JGAguado/LIA/enclosure/V1.0-Detachable/renders/explode-view.jpg

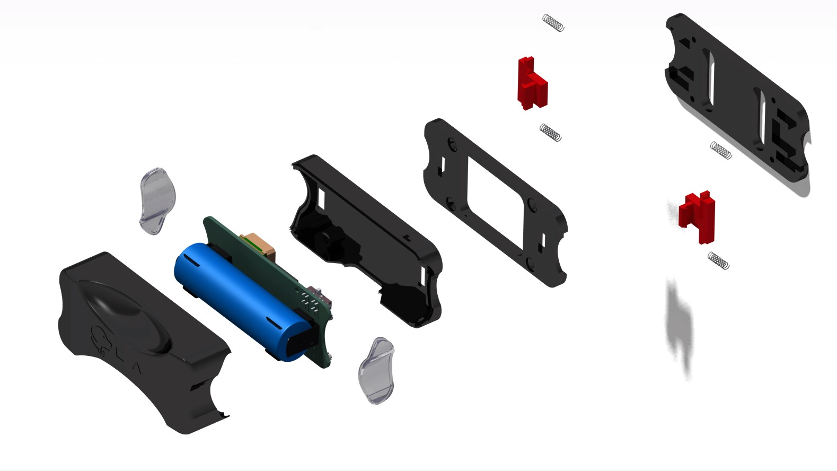
enclosure/V1.0-Detachable/renders/explode-view.jpg
