JGAguado/LIA/enclosure/V1.1-Fixed/renders/explode-view.jpg

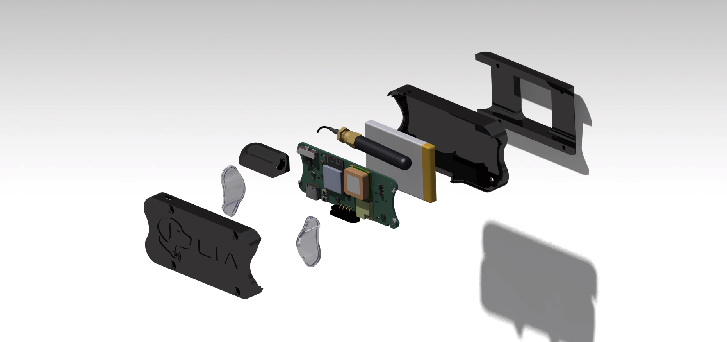
enclosure/V1.1-Fixed/renders/explode-view.jpg
