JGAguado/LIA/website/src/assets/brand/Primary dark.png

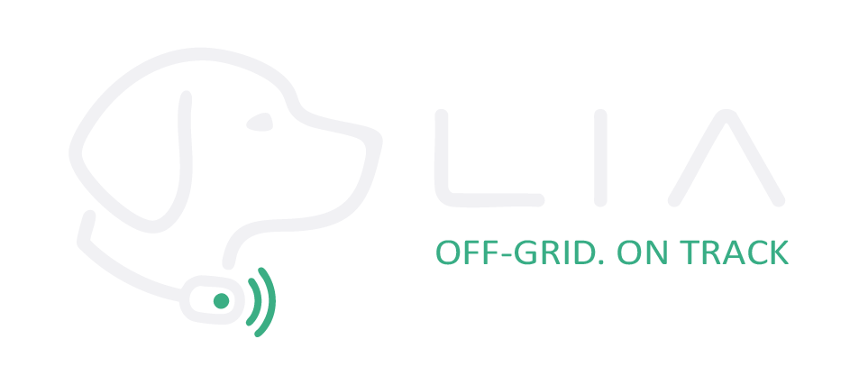
website/src/assets/brand/Primary dark.png
