JGAguado/LIA/website/src/assets/photos/6003601369522179307.jpg

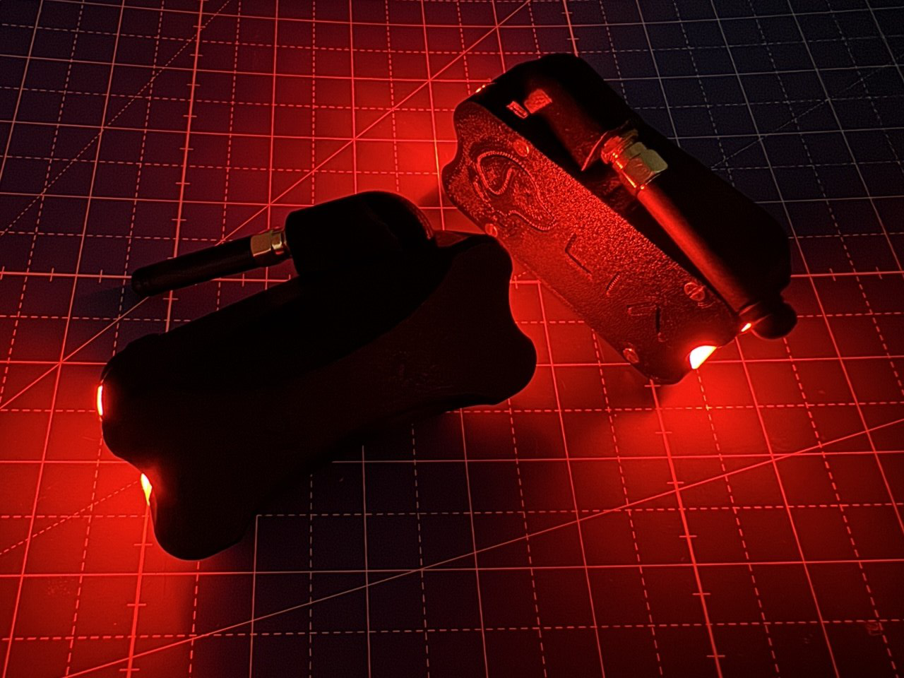
website/src/assets/photos/6003601369522179307.jpg
