JGAguado/LIA/website/src/assets/photos/6003601369522179308.jpg

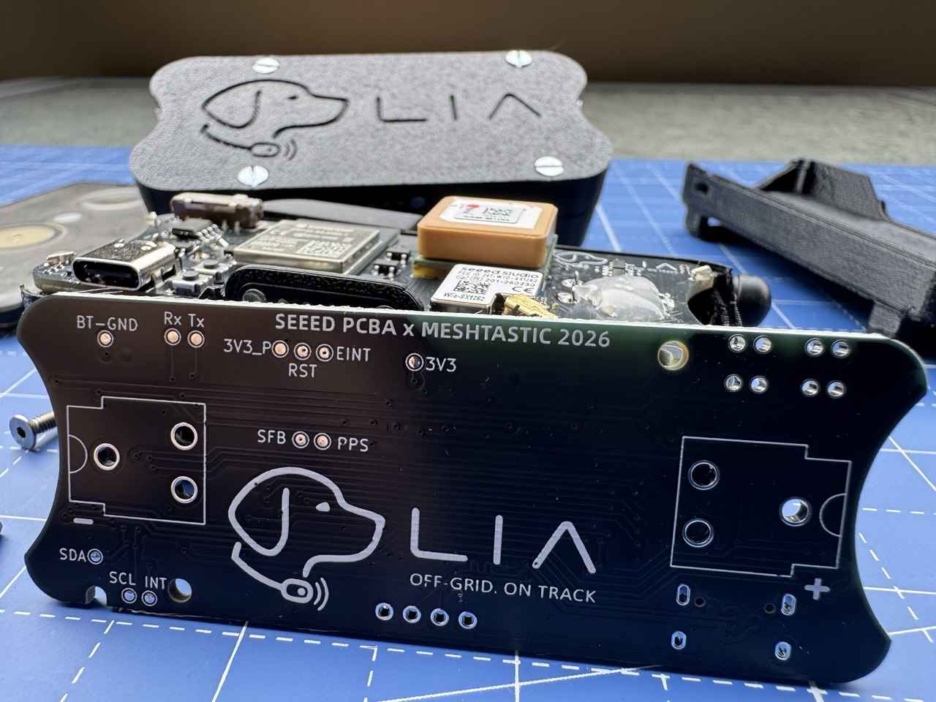
website/src/assets/photos/6003601369522179308.jpg
