JGAguado/LIA/website/src/assets/photos/6003601369522179309.jpg

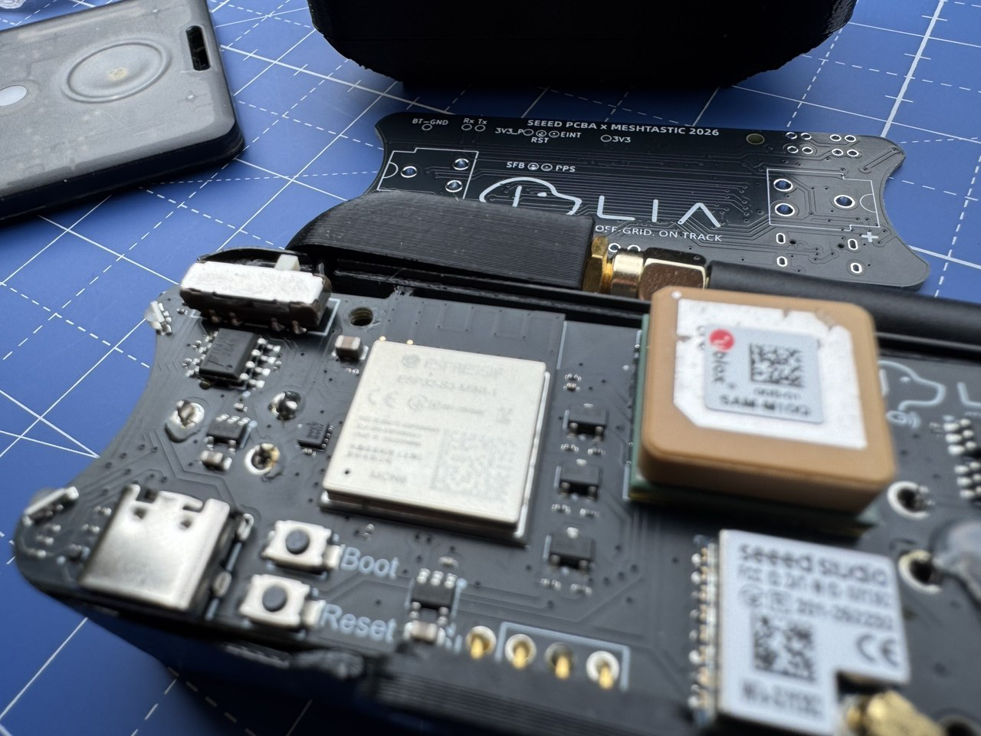
website/src/assets/photos/6003601369522179309.jpg
