JGAguado/LIA/website/src/assets/photos/6003601369522179310.jpg

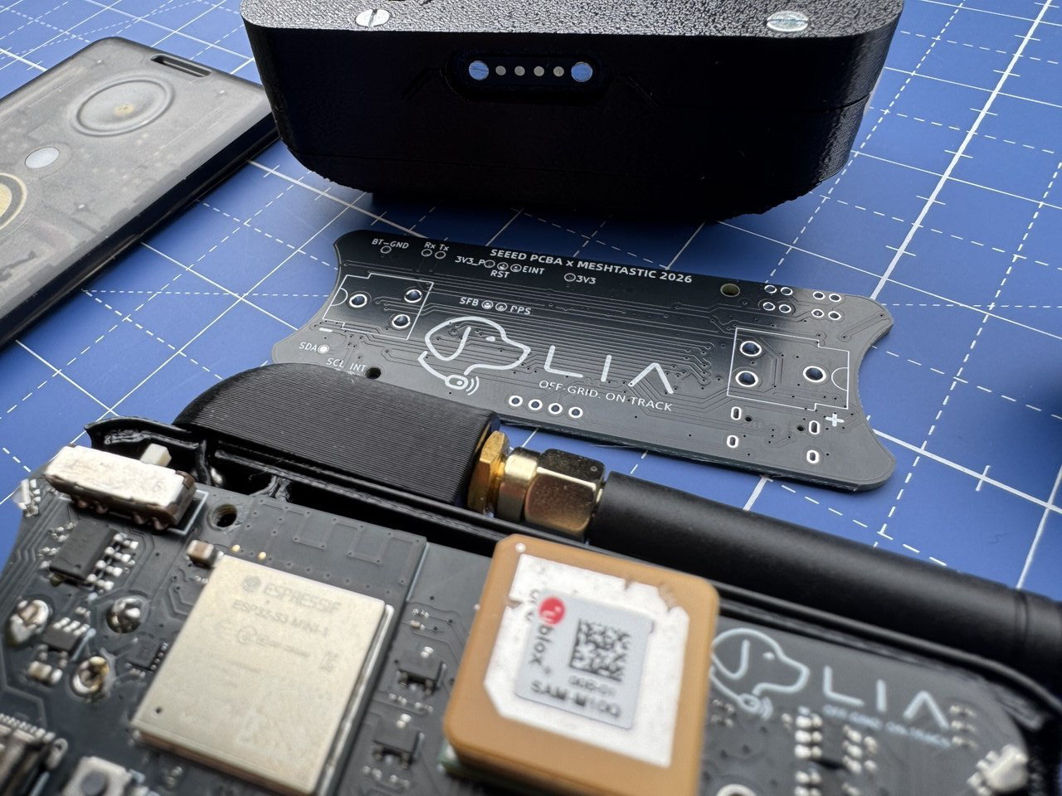
website/src/assets/photos/6003601369522179310.jpg
