JGAguado/LIA/website/src/assets/photos/6003601369522179314.jpg

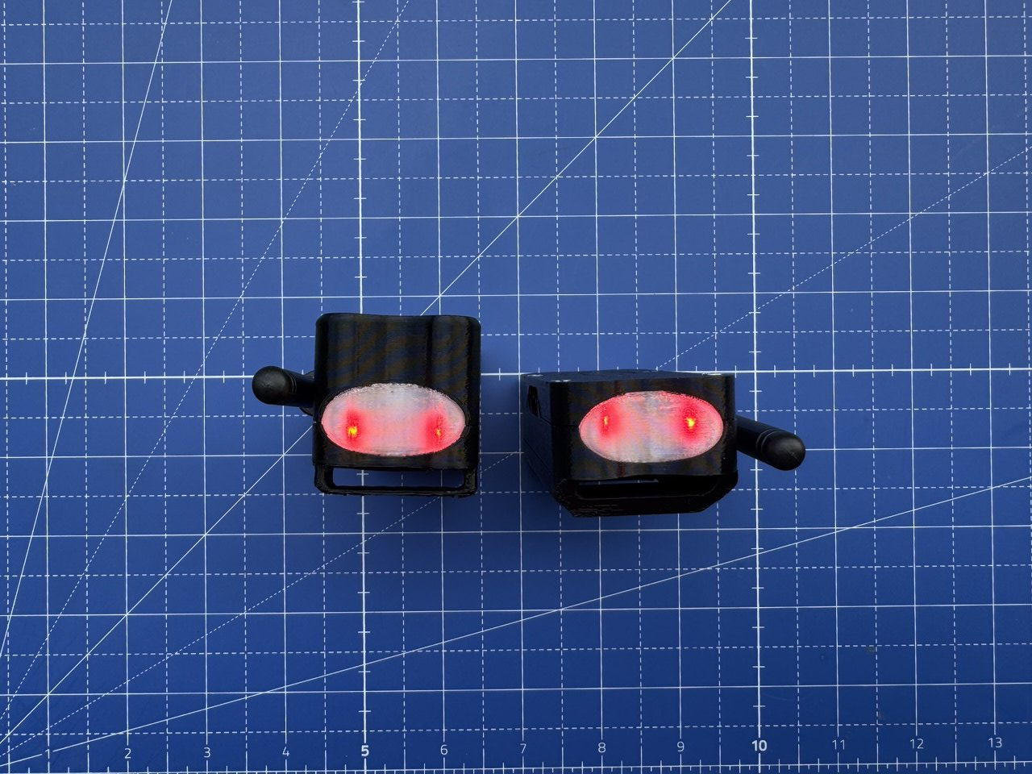
website/src/assets/photos/6003601369522179314.jpg
