JGAguado/LIA/website/src/assets/photos/6003601369522179320.jpg

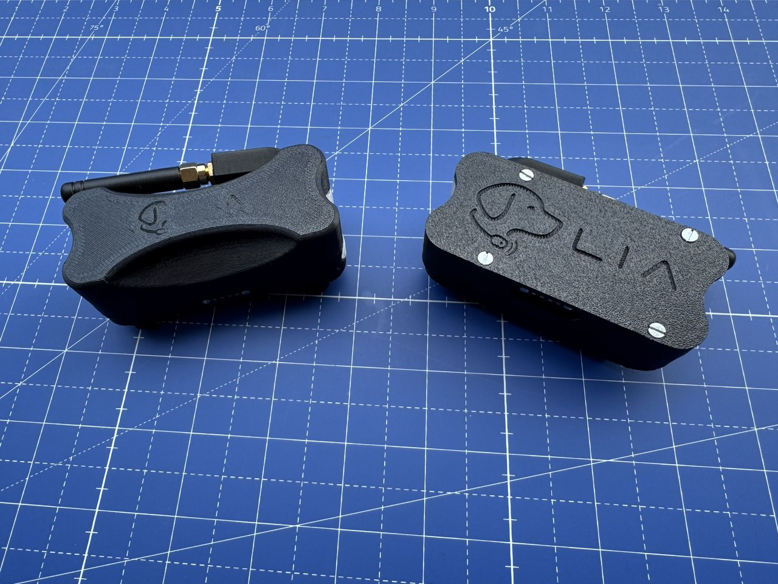
website/src/assets/photos/6003601369522179320.jpg
