JGAguado/LIA/website/src/assets/photos/6003601369522179321.jpg

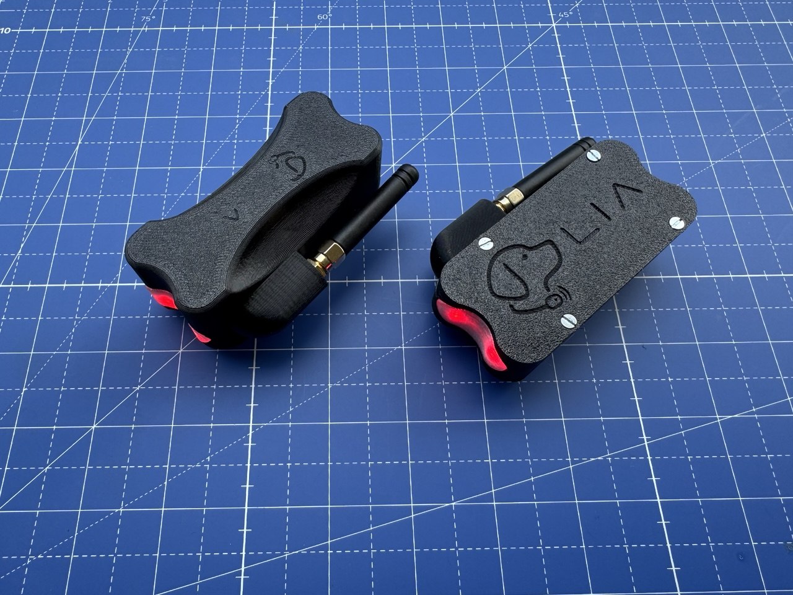
website/src/assets/photos/6003601369522179321.jpg
