JGAguado/LIA/website/src/assets/photos/Features/Beacon.jpg

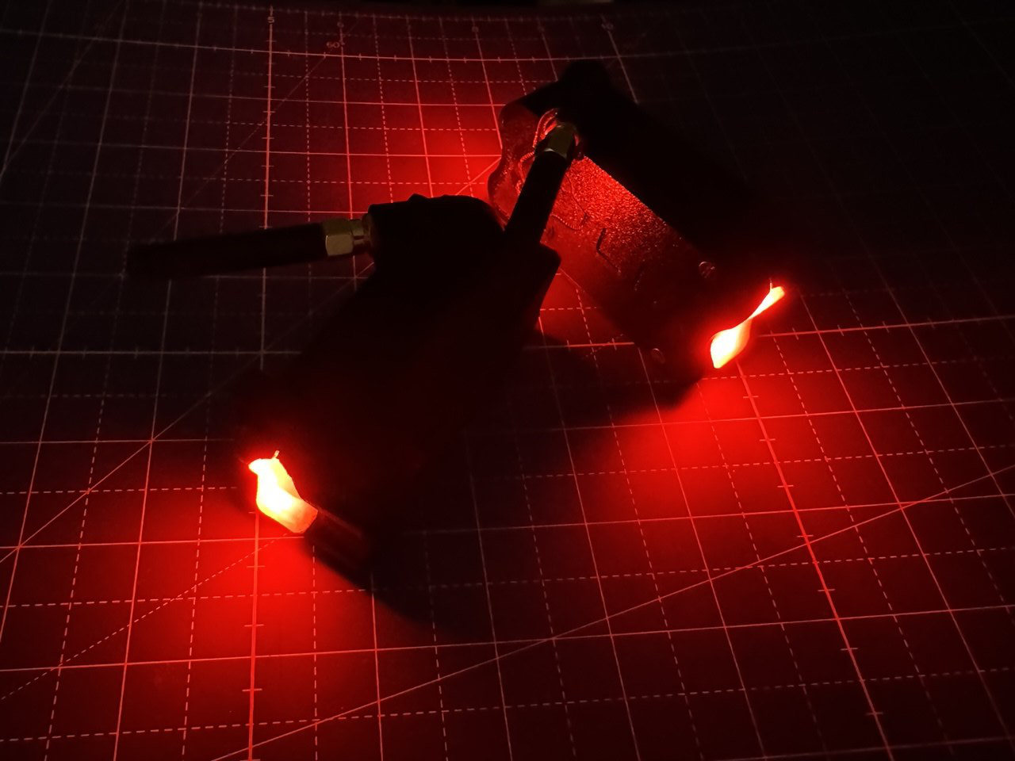
website/src/assets/photos/Features/Beacon.jpg
