JGAguado/LIA/website/src/assets/photos/Features/GPS.jpg

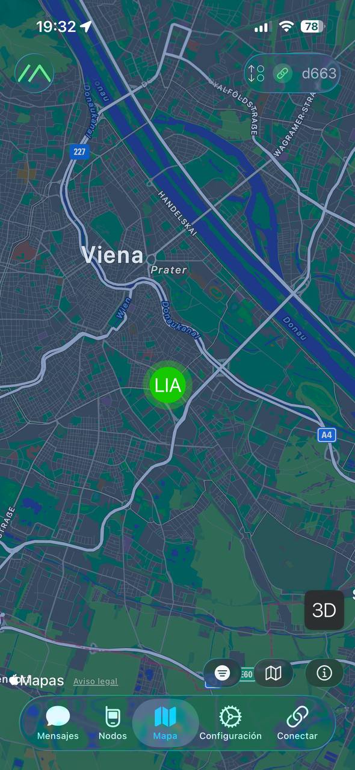
website/src/assets/photos/Features/GPS.jpg
