JGAguado/LIA/website/src/assets/photos/Features/Meshtastic.jpg

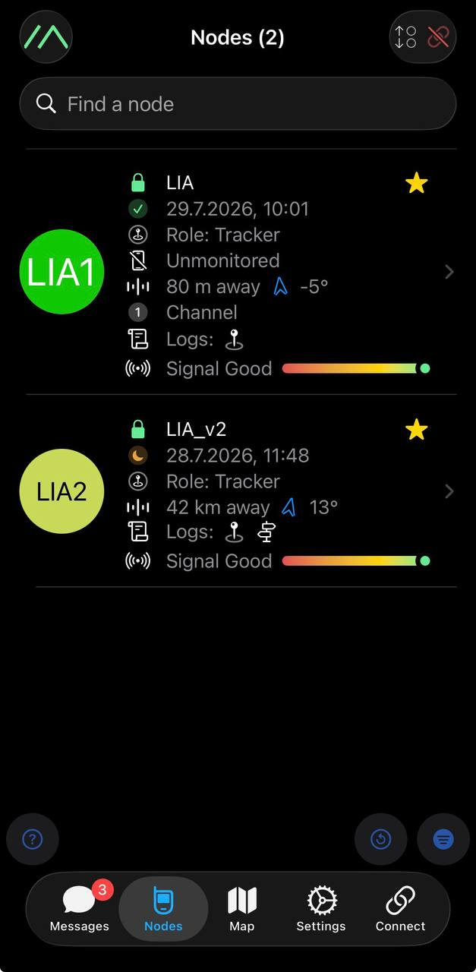
website/src/assets/photos/Features/Meshtastic.jpg
