JGAguado/LIA/website/src/assets/photos/Features/OpenSource.jpg

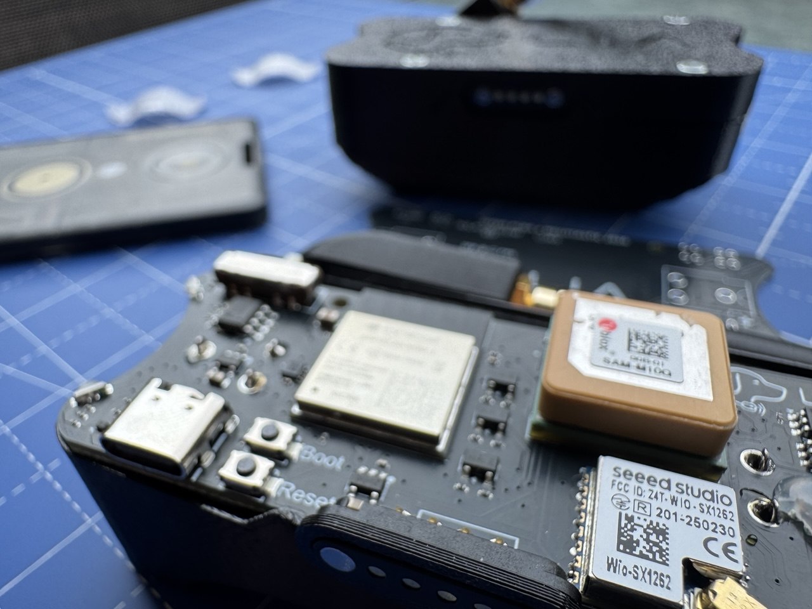
website/src/assets/photos/Features/OpenSource.jpg
