JGAguado/LIA/enclosure/V1.0-Detachable/renders/assembly-2.jpg

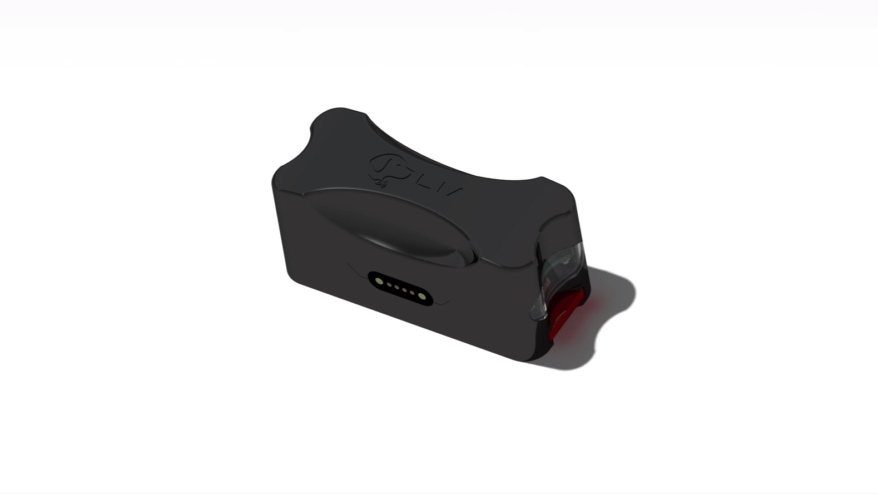
enclosure/V1.0-Detachable/renders/assembly-2.jpg
