JGAguado/LIA/enclosure/V1.1-Fixed/renders/assembly-1.jpg

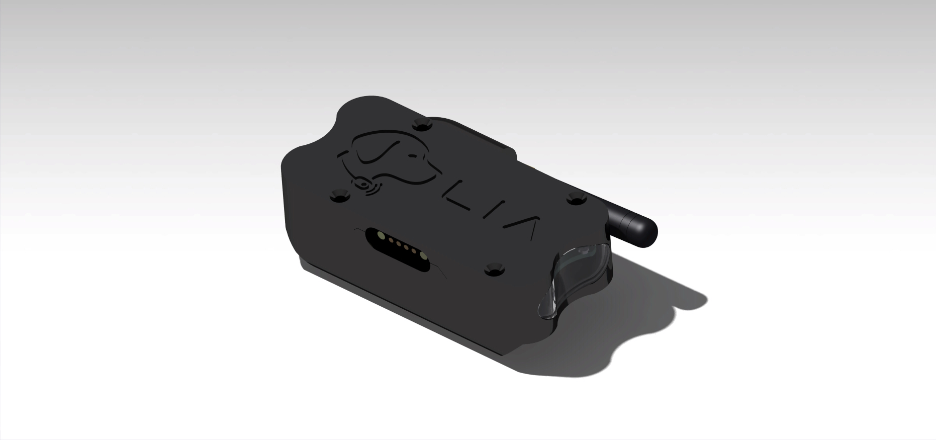
enclosure/V1.1-Fixed/renders/assembly-1.jpg
