JGAguado/LIA/enclosure/V1.1-Fixed/renders/assembly-2.jpg

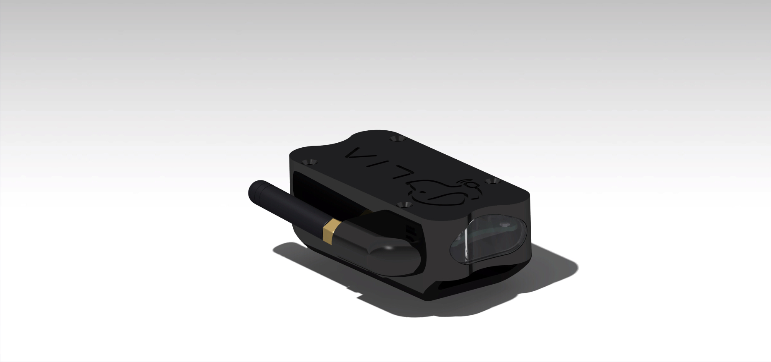
enclosure/V1.1-Fixed/renders/assembly-2.jpg
