JGAguado/LIA/website/src/assets/brand/Styleguide_1.png

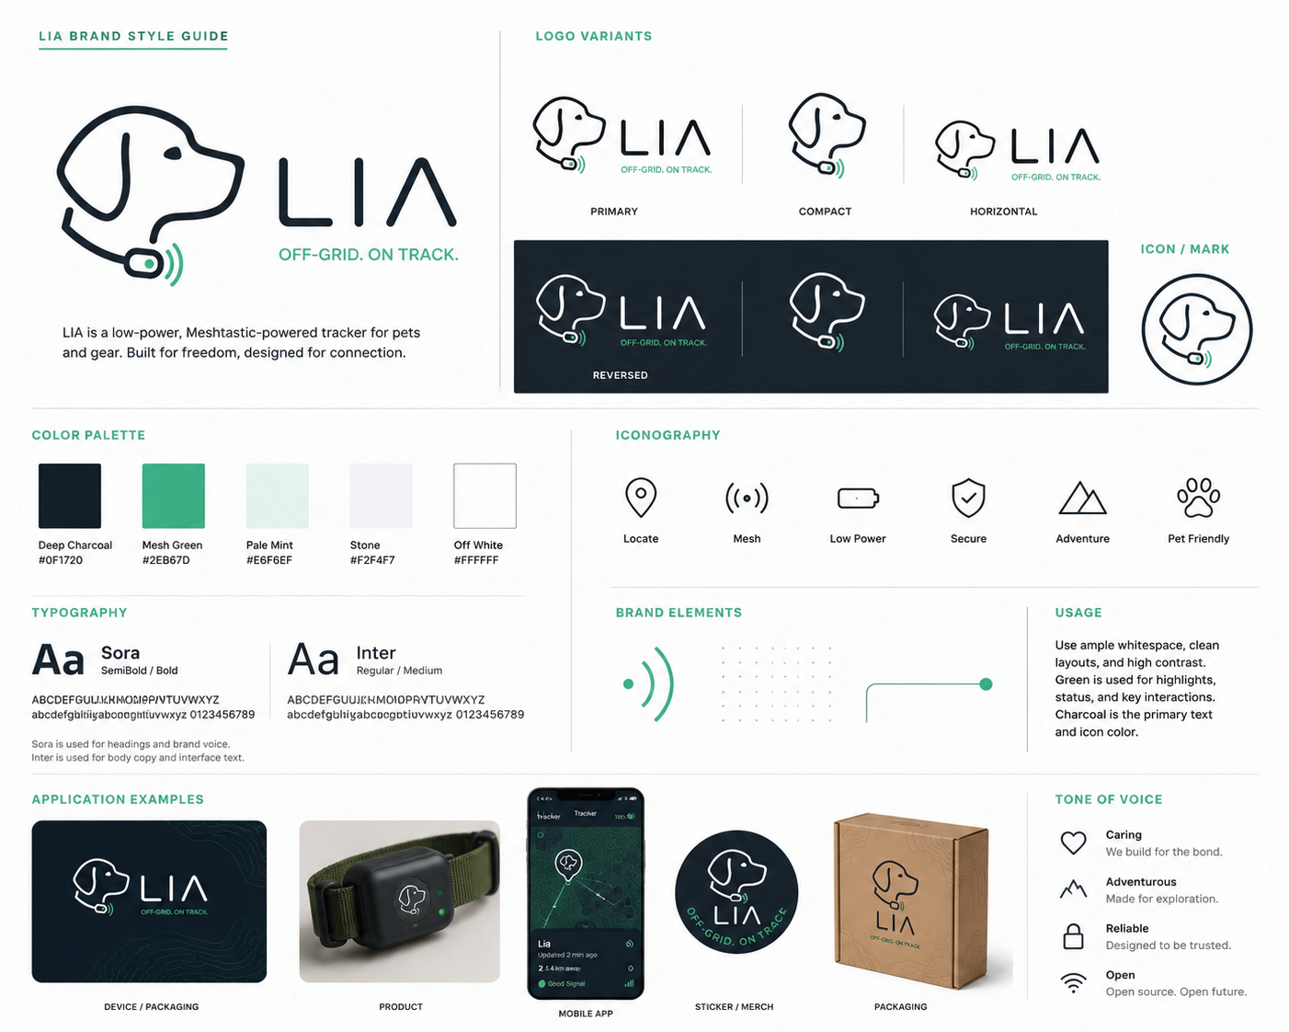
website/src/assets/brand/Styleguide_1.png
