JGAguado/LIA/website/src/assets/photos/IIC fix/1.jpg

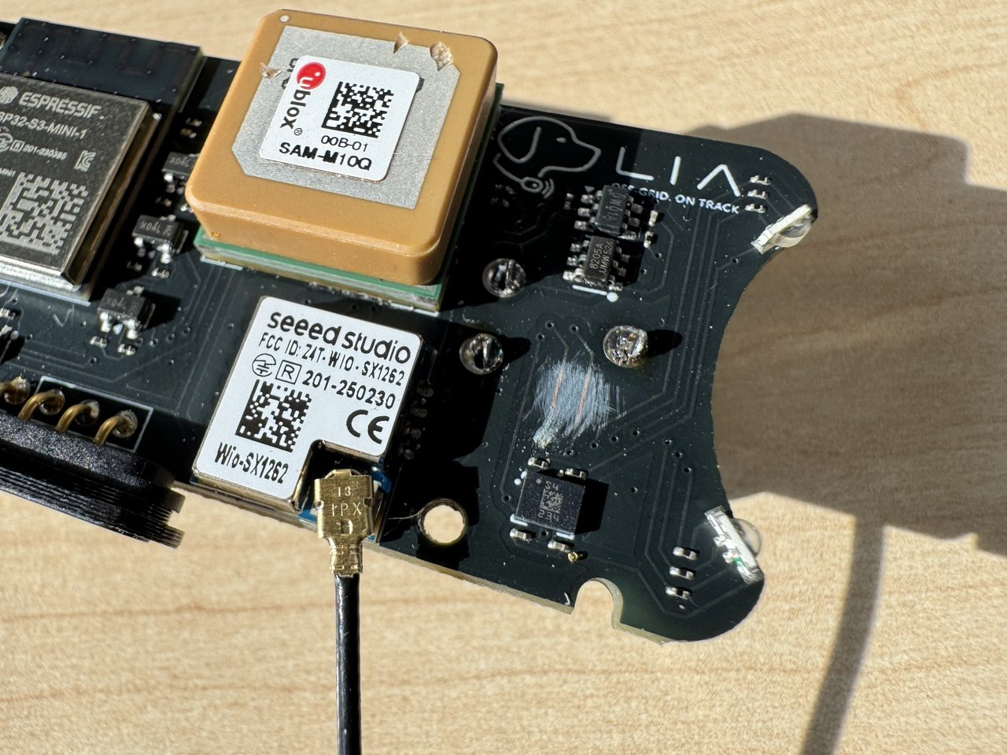
website/src/assets/photos/IIC fix/1.jpg
