JGAguado/LIA/website/src/assets/photos/IIC fix/2.jpg

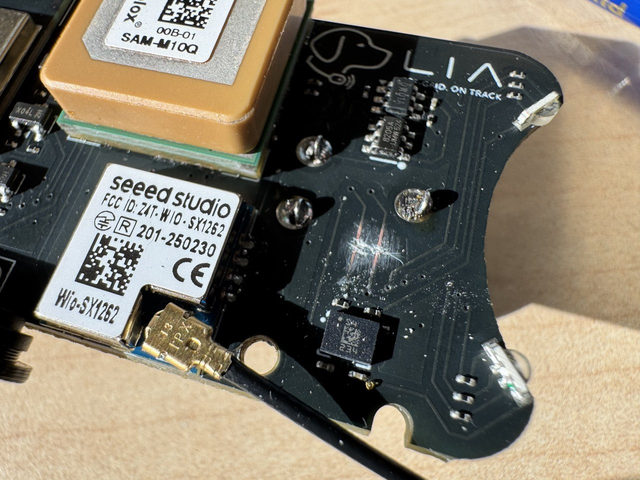
website/src/assets/photos/IIC fix/2.jpg
