JGAguado/LIA/website/src/assets/photos/IIC fix/3.jpg

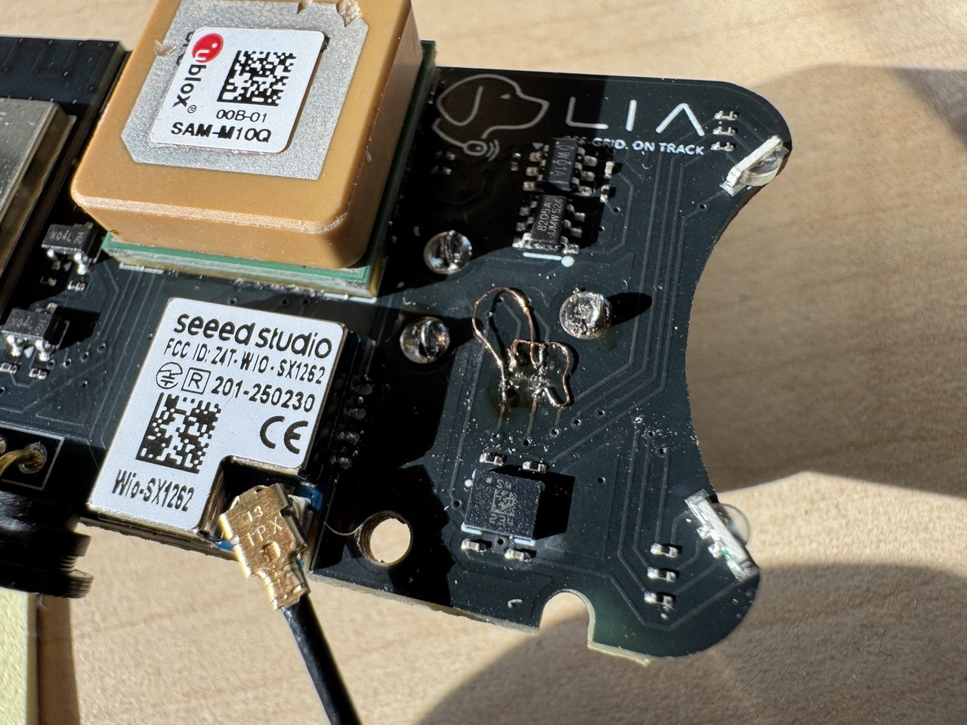
website/src/assets/photos/IIC fix/3.jpg
