JGAguado/LIA/website/src/assets/photos/IIC fix/4.jpg

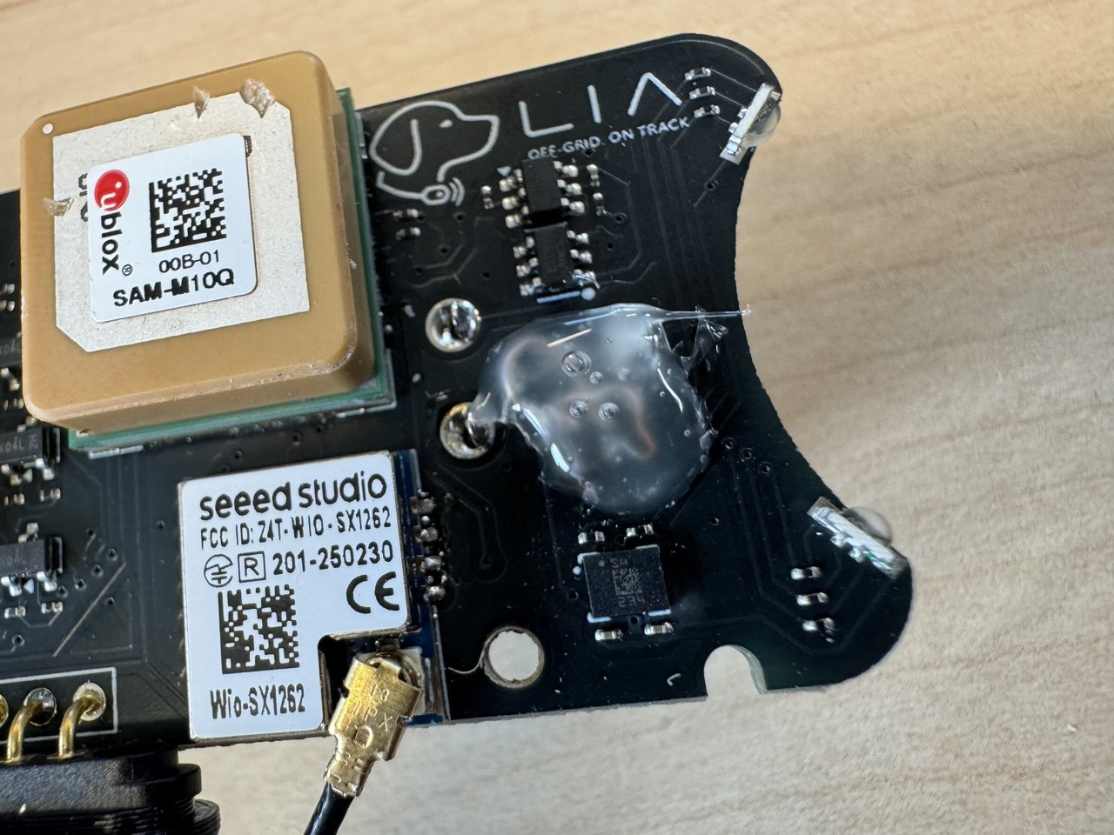
website/src/assets/photos/IIC fix/4.jpg
